sboettcher/lasertag/CADDesign/FinalDesigns/Handel/Griff_Akkuhalter.SLDPRT

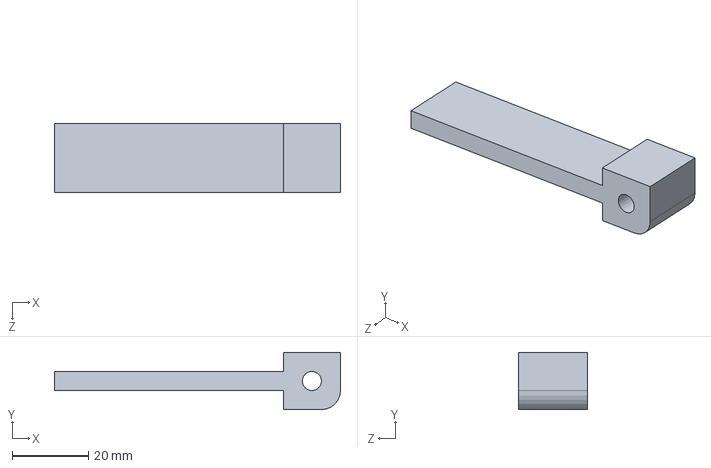
[picture p15: CAD file, 2015-03-04]
CADDesign/FinalDesigns/Handel/Griff_Akkuhalter.SLDPRT
75.0 x 15.0 x 18.0 mm
