sboettcher/lasertag/CADDesign/FinalDesigns/Other/Rohr.SLDPRT

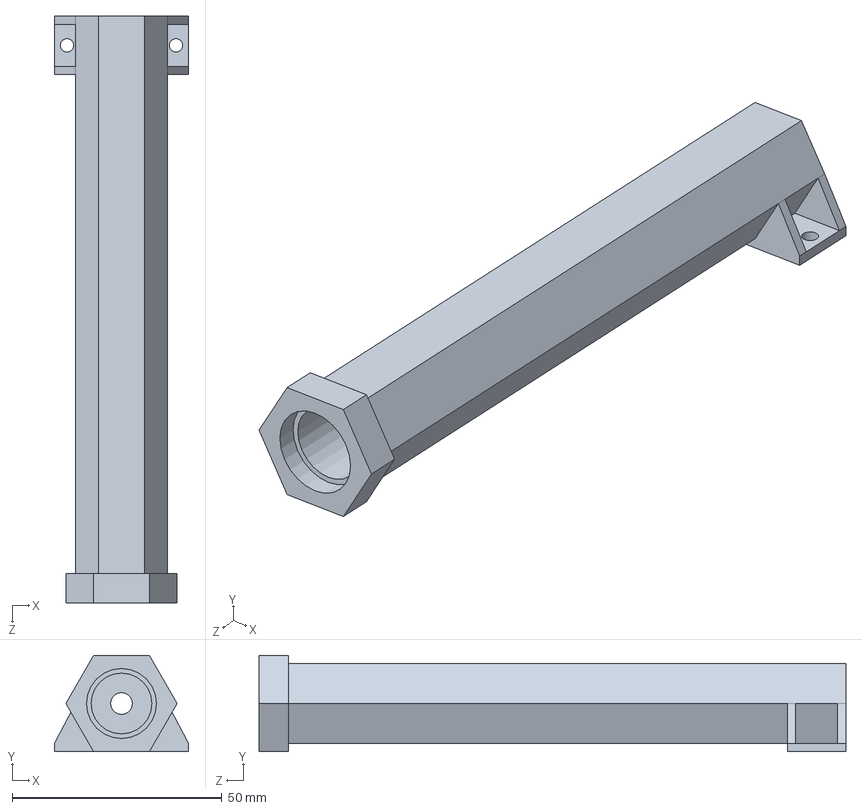
[picture p16: CAD file, 2015-03-04]
CADDesign/FinalDesigns/Other/Rohr.SLDPRT
32.0 x 23.0 x 140.0 mm
