sboettcher/lasertag/CADDesign/FinalDesigns/RFIDReader/Deckel.SLDPRT

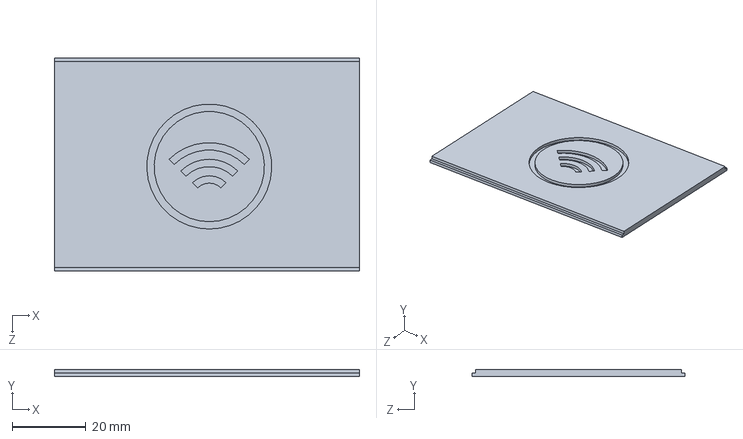
[picture p17: CAD file, 2015-03-04]
CADDesign/FinalDesigns/RFIDReader/Deckel.SLDPRT
83.0 x 2.00 x 58.0 mm
