sboettcher/lasertag/CADDesign/FinalDesigns/VestMaster/Gehaeuse.SLDPRT

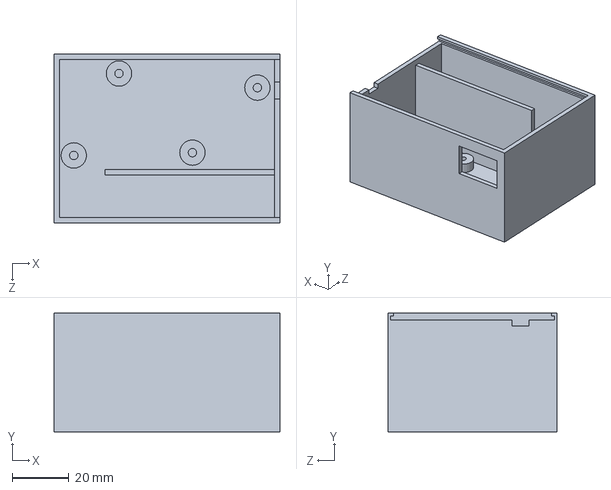
[picture p18: CAD file, 2015-03-04]
CADDesign/FinalDesigns/VestMaster/Gehaeuse.SLDPRT
80.0 x 42.0 x 60.0 mm
