sboettcher/lasertag/CADDesign/FinalDesigns/Components/Bluetooth_Tagger.SLDPRT

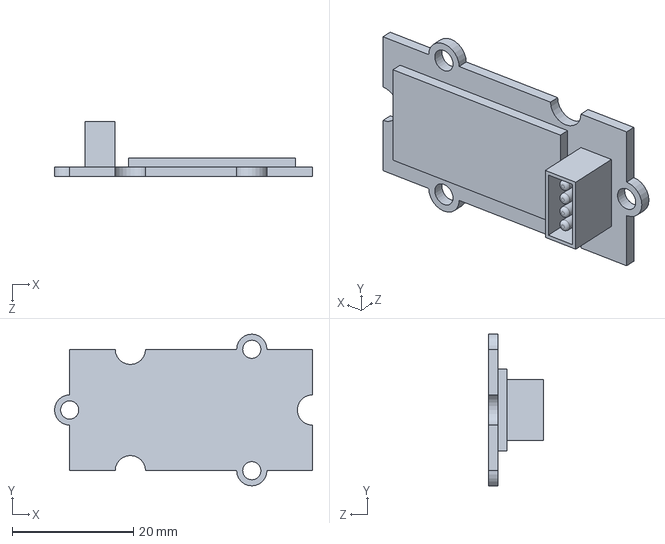
[picture p19: CAD file, 2015-03-04]
CADDesign/FinalDesigns/Components/Bluetooth_Tagger.SLDPRT
42.5 x 25.0 x 9.00 mm
