sboettcher/lasertag/CADDesign/FinalDesigns/Corpus/IRReceiver_Abdeckung.SLDPRT

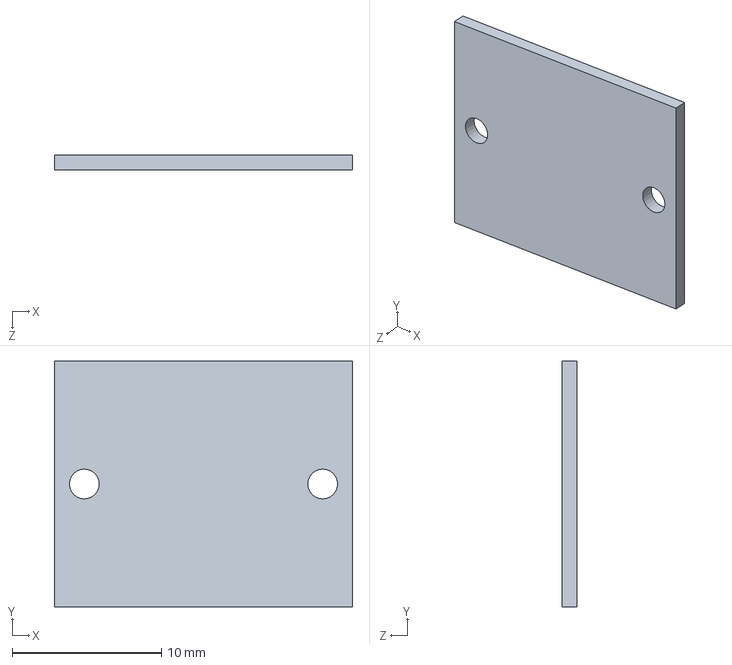
[picture p20: CAD file, 2015-03-04]
CADDesign/FinalDesigns/Corpus/IRReceiver_Abdeckung.SLDPRT
20.0 x 16.5 x 1.00 mm
