sboettcher/lasertag/CADDesign/FinalDesigns/DisplayHolder/Display_Holder_without_Tripod.SLDPRT

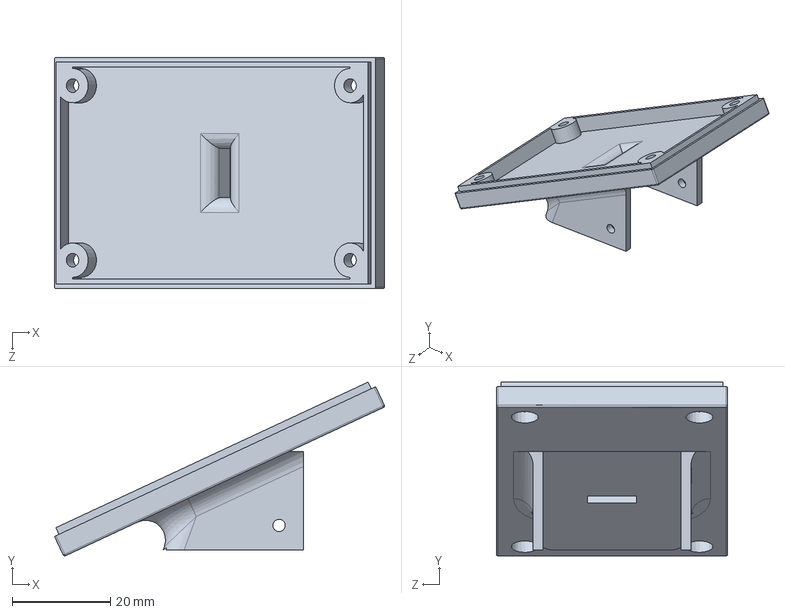
[picture p21: CAD file, 2015-03-04]
CADDesign/FinalDesigns/DisplayHolder/Display_Holder_without_Tripod.SLDPRT
67.0 x 35.3 x 47.0 mm
