sboettcher/lasertag/CADDesign/FinalDesigns/Handel/Griff_R_new.SLDPRT

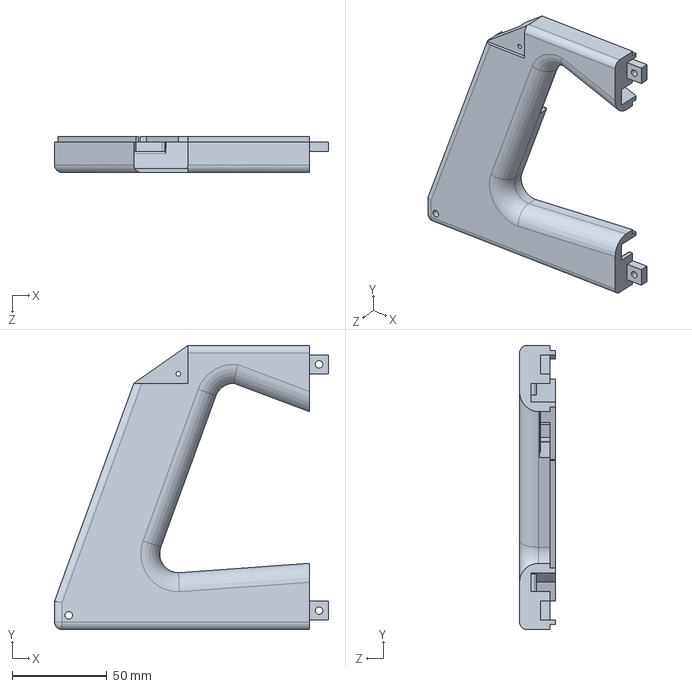
[picture p22: CAD file, 2015-03-04]
CADDesign/FinalDesigns/Handel/Griff_R_new.SLDPRT
144.6 x 150.0 x 19.0 mm
