sboettcher/lasertag/CADDesign/FinalDesigns/Other/Button.SLDPRT

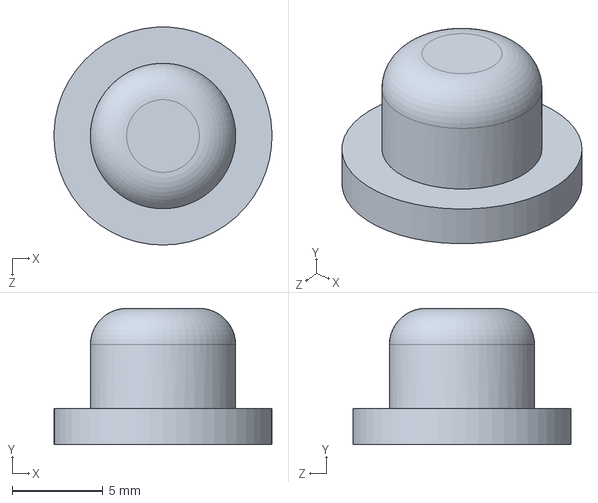
[picture p23: CAD file, 2015-03-04]
CADDesign/FinalDesigns/Other/Button.SLDPRT
12.0 x 7.50 x 12.0 mm
