sboettcher/lasertag/CADDesign/FinalDesigns/RailMount/RailMountKabel.SLDPRT

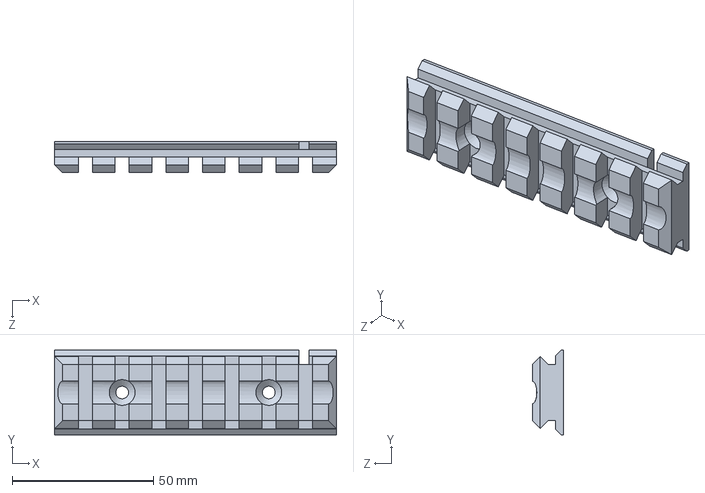
[picture p24: CAD file, 2015-03-04]
CADDesign/FinalDesigns/RailMount/RailMountKabel.SLDPRT
100.0 x 30.0 x 11.2 mm
