sboettcher/lasertag/CADDesign/FinalDesigns/VestMaster/Deckel.SLDPRT

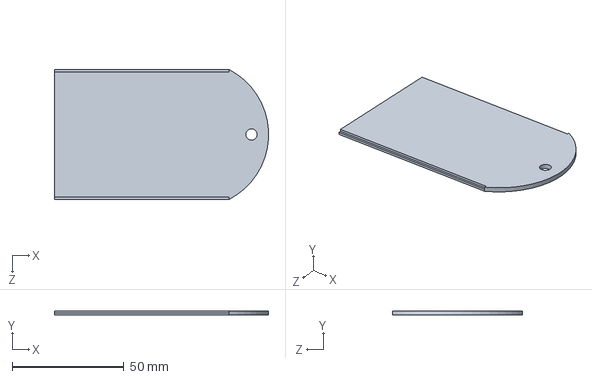
[picture p25: CAD file, 2015-03-04]
CADDesign/FinalDesigns/VestMaster/Deckel.SLDPRT
95.6 x 2.00 x 58.0 mm
