sboettcher/lasertag/CADDesign/FinalDesigns/Components/Display.SLDPRT

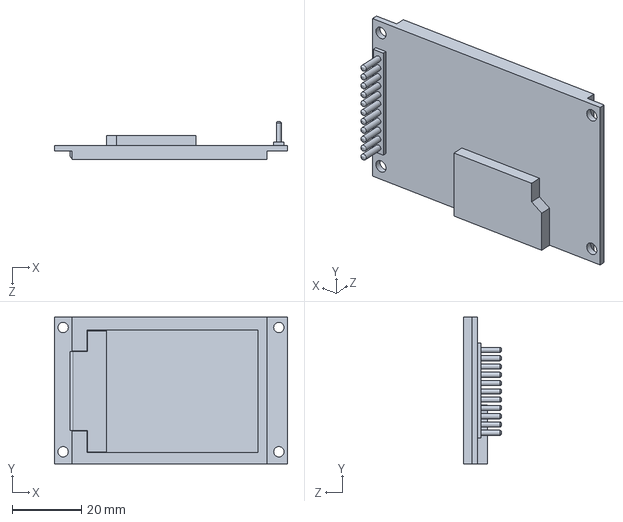
[picture p26: CAD file, 2015-03-04]
CADDesign/FinalDesigns/Components/Display.SLDPRT
67.5 x 42.5 x 11.0 mm
