sboettcher/lasertag/CADDesign/FinalDesigns/DisplayHolder/Display_Tripod.SLDPRT

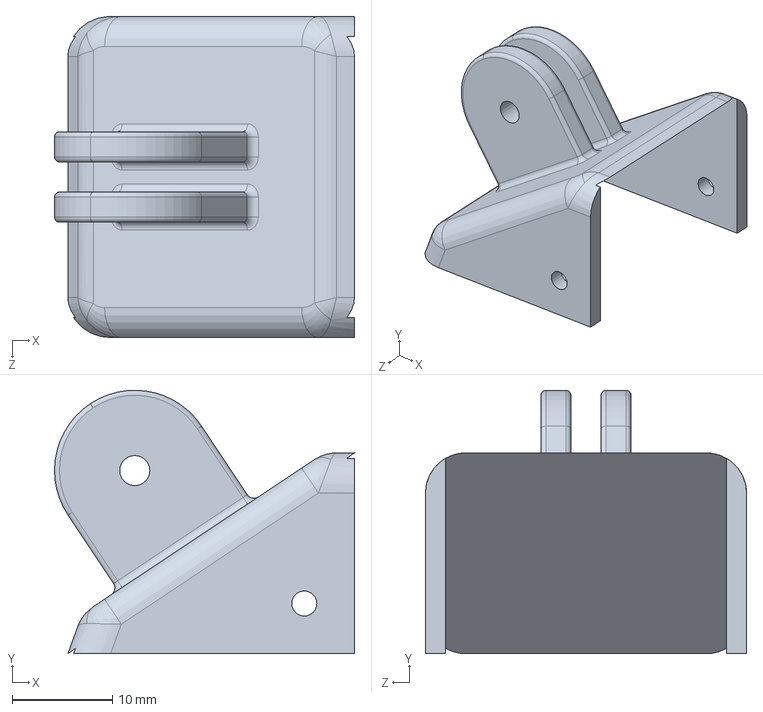
[picture p27: CAD file, 2015-03-04]
CADDesign/FinalDesigns/DisplayHolder/Display_Tripod.SLDPRT
29.9 x 26.2 x 32.0 mm
