sboettcher/lasertag/CADDesign/FinalDesigns/RailMount/RedDot-Sight2_Bottom.SLDPRT

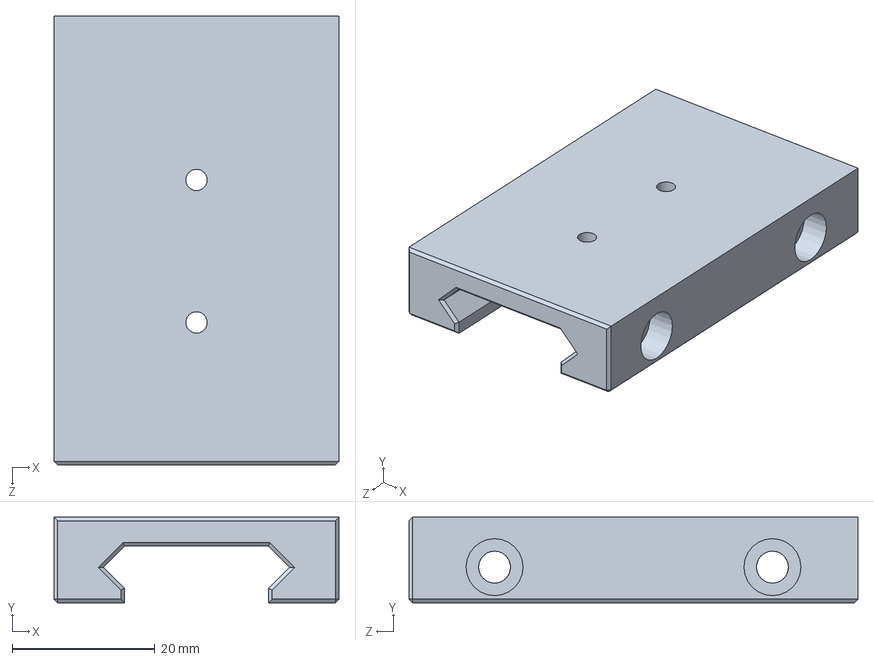
[picture p28: CAD file, 2015-03-04]
CADDesign/FinalDesigns/RailMount/RedDot-Sight2_Bottom.SLDPRT
40.0 x 12.0 x 63.0 mm
