sboettcher/lasertag/CADDesign/FinalDesigns/VestMaster/westMasterLid.SLDPRT

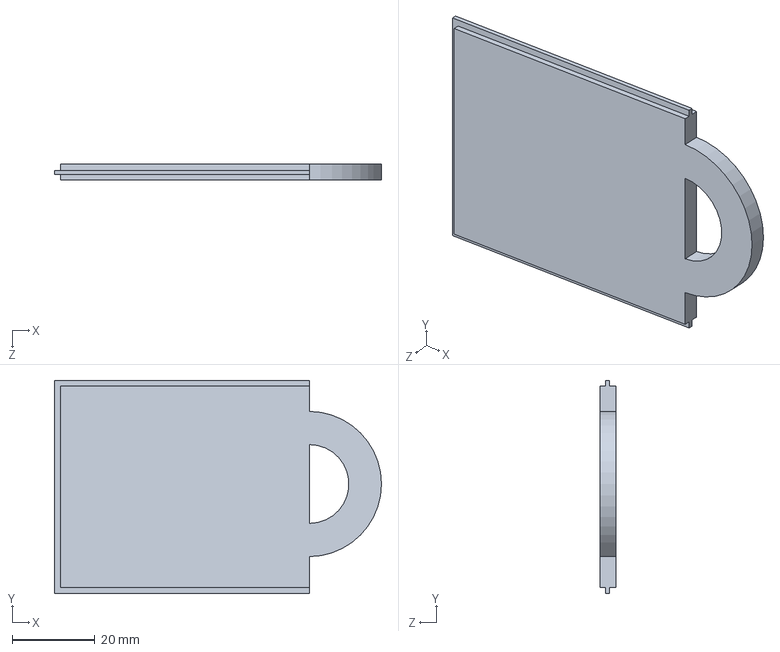
[picture p29: CAD file, 2015-03-04]
CADDesign/FinalDesigns/VestMaster/westMasterLid.SLDPRT
78.8 x 51.5 x 3.80 mm
