sboettcher/lasertag/CADDesign/FinalDesigns/RailMount/RedDot-Sight2_Top.SLDPRT

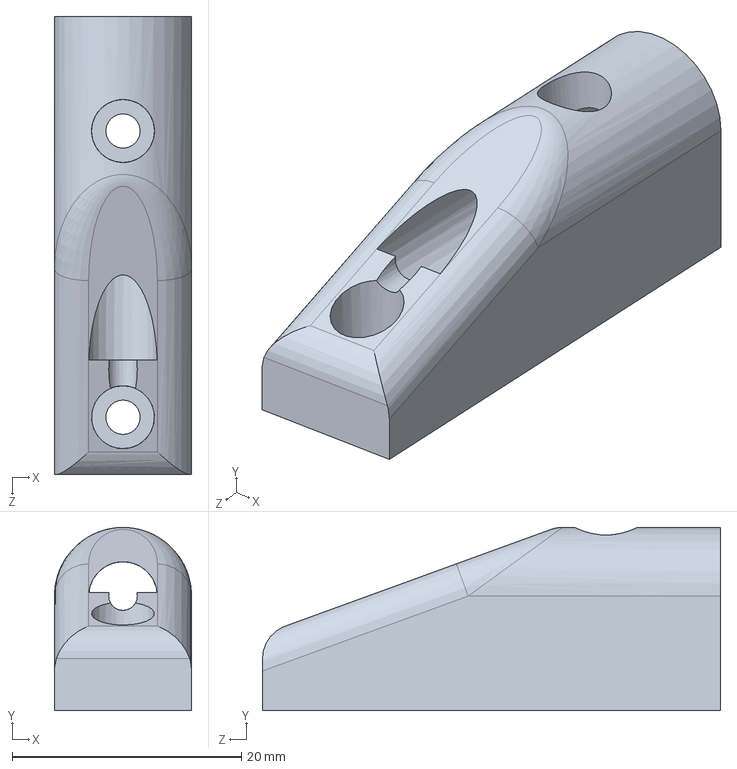
[picture p30: CAD file, 2015-03-04]
CADDesign/FinalDesigns/RailMount/RedDot-Sight2_Top.SLDPRT
12.0 x 16.0 x 40.0 mm
