sboettcher/lasertag/edison/src/lasertag.cpp

// Copyright 2015 Sebastian Boettcher

#include "./lasertag.h"

//________________________________________________________________________________
lasertag::lasertag()
  : m_dsp(NULL), m_i2c(NULL), m_gpio(NULL), m_bluetooth(NULL), m_client(NULL),
  m_i2c_bus(6), m_dsp_init(false), m_i2c_init(false),
  m_gpio_init(false), m_bt_init(false), m_tcp_init(false),
  m_bt_slave(""), m_active(false)
{
  m_hit_pos[0] = "Front";
  m_hit_pos[1] = "Back";
  m_hit_pos[2] = "Left";
  m_hit_pos[3] = "Right";
  m_hit_pos[100] = "Tagger";

  m_reset_time = 5;
}

//________________________________________________________________________________
lasertag::~lasertag() {
  delete m_i2c;
  delete m_gpio;
}



/*
 * I2C stuff
 */
 
//________________________________________________________________________________
void lasertag::i2c_init(int bus) {
  printf("[LASERTAG] init I2C on bus %d... ", m_i2c_bus);
  fflush(stdout);

  // make sure i2c bus number is 1 or 6
  if (bus != 1 && bus != 6) {
    printf("\n[LASERTAG] Wrong i2c bus number!. Using bus 6.\n");
  } else {
    m_i2c_bus = bus;
  }
  m_i2c = new mraa::I2c(m_i2c_bus);

  m_i2c_init = true;

  printf("Done.\n");
  fflush(stdout);

  i2c_write_int(I2C_BOOT, I2C_SEND_MSP);
}

//________________________________________________________________________________
uint8_t lasertag::i2c_read_int(uint8_t a) {
  if (!m_i2c_init)
    return 0;

  m_i2c->address(a);
  // read one integer from i2c bus and return it
  uint8_t rx_tx_buf[1];
  if (m_i2c->read(rx_tx_buf, 1) != 1) {
    printf("[LASERTAG] i2c read error!\n");
    fflush(stdout);
  }
  return rx_tx_buf[0];
  //return m_i2c->readByte();
}
//________________________________________________________________________________
void lasertag::i2c_write_int(uint8_t i, uint8_t a, bool start) {
  if (!m_i2c_init)
    return;

  m_i2c->address(a);
  if (start) {
    while(m_i2c->writeByte(I2C_START_BYTE) != MRAA_SUCCESS);
    usleep(100000);  // TODO: test if really necessary
  }
  while(m_i2c->writeByte(i) != MRAA_SUCCESS);
  usleep(100000);  // TODO: test if really necessary
  return;
}



/*
 * Display stuff
 */
 
//________________________________________________________________________________
void lasertag::dsp_init() {
  // constructor, init display, set rotation
  printf("[LASERTAG] init ILI9225... ");
  fflush(stdout);
  m_dsp = new TFT_22_ILI9225(TFT_CS_PIN, TFT_RST_PIN, TFT_RS_PIN);
  m_dsp->begin();
  m_dsp->setOrientation(0);
  printf("Done.\n");
  fflush(stdout);

  m_dsp_init = true;

  // draw the initial setup, fill status bars
  printf("[LASERTAG] draw init screen... ");
  fflush(stdout);
  dsp_draw_init();
  draw_health(0, m_player.get_max_health());
  draw_ammo(0, m_player.get_max_ammo());
  printf("Done.\n");
  fflush(stdout);
}

//________________________________________________________________________________
void lasertag::dsp_draw_init() {
  m_dsp->setFont(Terminal12x16);  // larger font

  //int fontX = m_dsp->fontX();
  int fontY = m_dsp->fontY();
  int maxX = m_dsp->maxX();
  int maxY = m_dsp->maxY();

  int barH = 25;

  m_h_coord[0] = 10;
  m_h_coord[1] = 35 + 3 * fontY;
  m_h_coord[2] = maxX - 10;
  m_h_coord[3] = m_h_coord[1] + barH;
  m_a_coord[0] = 10;
  m_a_coord[1] = m_h_coord[3] + 15 + fontY;
  m_a_coord[2] = maxX - 10;
  m_a_coord[3] = m_a_coord[1] + barH;

  // draw top part with placeholders for player name and current score
  m_dsp->drawText(10, 10, "[Player]");
  //m_dsp->drawText(maxX - 10 - 7 * fontX, 15 + fontY, "[Score]");
  m_dsp->drawText(10, 15 + fontY, "[Score]");
  m_dsp->drawLine(10, 20 + 2 * fontY, maxX - 10, 20 + 2 * fontY, COLOR_WHITE);

  // draw status bars
  m_dsp->drawText(10, 30 + 2 * fontY, "HEALTH:");
  m_dsp->drawRectangle(m_h_coord[0]-1, m_h_coord[1]-1, m_h_coord[2]+1, m_h_coord[3]+1, COLOR_WHITE);
  m_dsp->drawText(10, m_h_coord[3] + 10, "AMMO:");
  m_dsp->drawRectangle(m_a_coord[0]-1, m_a_coord[1]-1, m_a_coord[2]+1, m_a_coord[3]+1, COLOR_WHITE);

  // draw text boxes for hit, tagged status
  m_dsp->setFont(Terminal6x8);
  fontY = m_dsp->fontY();

  m_t_coord[0] = 10;
  m_t_coord[1] = m_a_coord[3] + 11 + fontY;
  m_t_coord[2] = maxX - 10;
  m_t_coord[3] = maxY - 5;

  m_dsp->drawText(10, m_a_coord[3] + 10, "hit by");
  m_dsp->drawText(maxX/2, m_a_coord[3] + 10, "tagged");
  m_dsp->drawRectangle(m_t_coord[0], m_t_coord[1], m_t_coord[2], m_t_coord[3], COLOR_WHITE);
  m_dsp->drawLine(maxX/2, m_t_coord[1], maxX/2, m_t_coord[3], COLOR_WHITE);
}



/*
 * other initializations
 */
 
//________________________________________________________________________________
void lasertag::bt_init() {
  if (m_bt_slave == "")
    return;

  m_bluetooth = new edison_serial("/dev/ttyMFD1", B38400);  // UART1, bt module needs 38400 baud
  m_bluetooth->bt_master_init("EdisonBTMaster01", m_bt_slave);
  
  printf("\n");
  fflush(stdout);

  m_threads.push_back(std::thread(&lasertag::t_read_bt, this));

  m_bt_init = true;
}

//________________________________________________________________________________
void lasertag::tcp_init(std::string address) {
  m_client = new tcp_client;
  if (m_client->tcp_connect(address))
    m_tcp_init = true;
}

//________________________________________________________________________________
void lasertag::gpio_init(int pin) {
  m_gpio = new mraa::Gpio(pin);
  if (m_gpio == NULL) {
    printf("[LASERTAG] gpio init failed.\n");
    fflush(stdout);
    return;
  }

  mraa_result_t response;
  response = m_gpio->dir(mraa::DIR_IN);
  if (response != MRAA_SUCCESS) {
    mraa::printError(response);
    return;
  }

  m_gpio_init = true;
}



/*
 * Functions called as threads. These handle all the IO stuff etc.
 */

//________________________________________________________________________________
void lasertag::t_read_i2c() {
  uint8_t i2c_rec = 0;

  std::vector<std::future<void>> handles;  // collect all handles for async calls
  while (m_active) {
    if (!m_i2c_init)
      continue;

    // read from rec i2c
    i2c_rec = i2c_read_int(I2C_REC_MSP);
    // filter out idle, error bytes
    if (i2c_rec != 0 && i2c_rec != 255) {
      // asynchronously call hitreg function so i2c communication can continue during
      handles.push_back(std::async(std::launch::async, &lasertag::hit_register, this, i2c_rec, 100));
    }

    // read from send i2c
    i2c_rec = i2c_read_int(I2C_SEND_MSP);
    //if (i2c_rec != 0) {
    //  printf("recieved %d\n", i2c_rec);
    //  fflush(stdout);
    //}
    if (i2c_rec == I2C_TRIGGER) {
      if (m_player.get_ammo() > 0) {
        // decrement ammo on trigger activation
        int old = m_player.fired();
        // asynchronously draw on display so tcp communication can continue
        handles.push_back(std::async(std::launch::async, &lasertag::draw_ammo, this, old, m_player.get_ammo()));
        // write current ammo to server
        std::stringstream ss;
        ss << "<as:" << m_player.get_ammo() << ">\n";
        if (m_tcp_init && m_client->connected())
          m_client->tcp_send(ss.str());
        if (m_player.get_ammo() == 0) {
          i2c_write_int(I2C_NO_AMMO, I2C_SEND_MSP);
          handles.push_back(std::async(std::launch::async, &lasertag::reset_ammo, this));
        }
      }
    }
    usleep(1000);
  }
  for (auto& h : handles) h.get();  // make sure all async calls return
}

//________________________________________________________________________________
void lasertag::t_read_bt() {
  int bt_rec = 0;
  int code = 0;
  int pos = 0;

  uint8_t idx = 0;

  std::vector<std::future<void>> handles;  // collect all handles for async calls
  while (m_active) {
    if (!m_bt_init || !m_bluetooth->bt_connected())
      continue;
    while (m_bluetooth->available(0,1000)) {
      // read byte from bluetooth serial
      bt_rec = (uint8_t)m_bluetooth->serial_read();
      if (bt_rec == SERIAL_START_BYTE) {  // indicates new hit, read next 2 bytes for code and position
        idx = 1;
      } else if (idx == 1) {
        code = bt_rec;
        idx = 2;
      } else if (idx == 2) {
        pos = bt_rec;
        idx = 0;
        // asynchronously call hitreg function so bt communication can continue during
        handles.push_back(std::async(std::launch::async, &lasertag::hit_register, this, code, pos));
      }
      bt_rec = 0;
    }
  }
  for (auto& h : handles) h.get();  // make sure all async calls return
}

//________________________________________________________________________________
void lasertag::t_read_tcp() {
  while (m_active) {
    if (!m_tcp_init || !m_client->connected())
      continue;
    if (m_client->tcp_available(0, 1000) > 0) {
      // read string from tcp, doesn't return terminating characters
      std::string tcp_rec = m_client->tcp_read_string("\n");
      parse_cmd(tcp_rec);
    }
  }
}

//________________________________________________________________________________
void lasertag::t_read_gpio() {
  std::vector<std::future<void>> handles;  // collect all handles for async calls
  while (m_active) {
    if (m_gpio_init && m_gpio->read() == 0) {
      if (m_player.get_ammo() > 0) {
        // decrement ammo on trigger activation
        int old = m_player.fired();
        // asynchronously draw on display so tcp communication can continue
        handles.push_back(std::async(std::launch::async, &lasertag::draw_ammo, this, old, m_player.get_ammo()));
      }
      usleep(100000);  // wait some time so tagger can't trigger continuously
    }
  }
  for (auto& h : handles) h.get();  // make sure all async calls return
}



/*
 * Threading management
 */
 
//________________________________________________________________________________
void lasertag::spawn_threads() {
  printf("[LASERTAG] Spawning threads.\n");
  fflush(stdout);
  m_active = true;
  m_threads.push_back(std::thread(&lasertag::t_read_i2c, this));
  //m_threads.push_back(std::thread(&lasertag::t_read_bt, this));  // only spawn if vest used
  m_threads.push_back(std::thread(&lasertag::t_read_tcp, this));
  //m_threads.push_back(std::thread(&lasertag::t_read_gpio, this));  // now handled by msp sending 's' via i2c
  printf("[LASERTAG] Done.\n");
  fflush(stdout);
}

//________________________________________________________________________________
void lasertag::join_threads() {
  printf("[LASERTAG] Joining threads.\n");
  fflush(stdout);
  m_active = false;
  for (auto& th : m_threads) th.join();
  m_threads.clear();
  printf("[LASERTAG] Done.\n");
  fflush(stdout);
}



/*
 * Gameplay functions
 */

//________________________________________________________________________________
void lasertag::hit_register(int code, int pos) {
  if (m_player.get_health() == 0)
    return;

  if (code == m_player.get_ID())
    return;

  // make sure there is only one execution of the function at a time
  std::lock_guard<std::recursive_mutex> hitreg_lock(m_mtx_hitreg);
  printf("[LASERTAG] Hit by %i at %i\n", code, pos);
  fflush(stdout);
  
  // send the player code to the server to recieve player name
  std::stringstream ss;
  ss << "<hi:" << code << ":" << pos << ">\n";
  if (m_tcp_init && m_client->connected())
    m_client->tcp_send(ss.str());

  // decrement health by one
  if (m_player.get_health() > 0) {
    int old = m_player.hit();
    draw_health(old, m_player.get_health());
  }

  // write hit position to display
  clear_hit_pos();
  std::stringstream text;
  //text << code << " -> " << pos;
  if (m_hit_pos.count(pos) == 0) {
    text << "N/A";
  } else {
    text << m_hit_pos[pos];
  }
  dsp_write(m_t_coord[0] + 5, m_t_coord[1] + 5, text.str());

  if (m_player.get_health() == 0) {
    i2c_write_int(I2C_NO_HEALTH, I2C_SEND_MSP);
    reset_health();
  }
}

//________________________________________________________________________________
void lasertag::parse_cmd(std::string cmd) {
  std::vector<std::future<void>> handles;  // collect all handles for async calls

  printf("%s\n", cmd.c_str());
  fflush(stdout);

  if (cmd.find("<") == std::string::npos || cmd.find(">") == std::string::npos)
    return;

  // command structure: <key:data>
  // get the command key
  std::string key = cmd.substr(cmd.find("<") + 1, cmd.find(":") - 1);

  // filter leading exclamation point from key that the server might send
  if (key.find("!") != std::string::npos)
    key = key.substr(key.find("!"), 1);

  if (key == "")
    return;

  // get the command data
  std::string data = cmd.substr(cmd.find(":") + 1, cmd.find(">") - 1 - cmd.find(":"));
  if (data == "")
    return;

  if (key == "ci") {  // <ci:has_vest:id>
    m_player.set_vest(std::stoi(data.substr(0, 1)));
    m_player.set_ID(std::stoi(data.substr(2)));
    std::stringstream ss;
    ss << "vest" << std::to_string(m_player.get_ID());
    m_bt_slave = ss.str();
    if (m_player.get_vest()) {
      bt_init();
      usleep(2000000);  // 2 sec wait for safety, might not be needed
      set_team_color(m_player.get_color());
    }
    // transmit ID to msp
    if (m_i2c_init) {
      i2c_write_int(I2C_PLAYER_CODE, I2C_SEND_MSP);
      i2c_write_int(m_player.get_ID(), I2C_SEND_MSP, false);
      //i2c_write_int(0xFF, I2C_REC_MSP, false);
      //i2c_write_int(0x00, I2C_REC_MSP, false);
      //i2c_write_int(m_player.get_ID(), I2C_REC_MSP, false);
      //i2c_write_int(0xFE, I2C_REC_MSP, false);
    }
  } else if (key == "np") {  // <np:playername>
    m_player.set_name(data);
    write_name();
  } else if (key == "in") {
    write_info(data, 2);
    write_name();
  } else if (key == "ts") {  // <ts:teamcolor>
    if (data == "red") {
      m_player.set_color(COLOR_RED);
    } else if (data == "green") {
      m_player.set_color(COLOR_GREEN);
    } else if (data == "blue") {
      m_player.set_color(COLOR_BLUE);
    } else if (data == "none") {
      m_player.set_color(COLOR_WHITE);
    }
    set_team_color(m_player.get_color());
    write_name();
  } else if (key == "hs") {  // <hs:health>
    int old = m_player.set_health(std::stoi(data));
    draw_health(old, m_player.get_health());
  } else if (key == "ps") {  // <ps:score>
    m_player.set_score(std::stoi(data));
    write_score();
  } else if (key == "as") {  // <as:ammo>
    int old = m_player.set_ammo(std::stoi(data));
    draw_ammo(old, m_player.get_ammo());
  } else if (key == "ap") {  // <ap:ammo_per>
    m_player.set_ammo_per(std::stoi(data));
  } else if (key == "hd") {  // <hd:health_decrease>
    m_player.set_health_per(std::stoi(data));
  } else if (key == "hi") {  // <hi:tagged:pos>
    std::string name = data.substr(0, data.find(":"));
    std::string pos = data.substr(data.find(":") + 1);
    printf("[LASERTAG] Tagged player %s at %s\n", name.c_str(), pos.c_str());
    fflush(stdout);
    clear_tagged_pos();
    clear_tagged_name();
    // asynchronously draw on display so tcp communication can continue
    // TODO: check for string length, should fit in box
    handles.push_back(std::async(std::launch::async, &lasertag::dsp_write, this, m_dsp->maxX()/2 + 5, m_t_coord[1] + 5, pos, Terminal6x8, COLOR_WHITE));
    handles.push_back(std::async(std::launch::async, &lasertag::dsp_write, this, m_dsp->maxX()/2 + 5, m_t_coord[1] + 15, name, Terminal11x16, COLOR_WHITE));
  } else if (key == "hp") {  // <hp:hit_by>
    printf("[LASERTAG] Hit by %s \n", data.c_str());
    fflush(stdout);
    clear_hit_name();
    // asynchronously draw on display so tcp communication can continue
    // TODO: check for string length, should fit in box
    handles.push_back(std::async(std::launch::async, &lasertag::dsp_write, this, m_t_coord[0] + 5, m_t_coord[1] + 15, data, Terminal11x16, COLOR_WHITE));
  } else if (key == "hv") {  // <hv:tagged_name>
    printf("[LASERTAG] Tagged player %sn", data.c_str());
    fflush(stdout);
    clear_tagged_name();
    // asynchronously draw on display so tcp communication can continue
    // TODO: check for string length, should fit in box
    handles.push_back(std::async(std::launch::async, &lasertag::dsp_write, this, m_dsp->maxX()/2 + 5, m_t_coord[1] + 15, data, Terminal11x16, COLOR_WHITE));
  } else if (key == "at") {  // <at:tagger_active>
    if (data == "0") {
      i2c_write_int(I2C_DEACTIVATE, I2C_SEND_MSP);
    } else if (data == "1") {
      i2c_write_int(I2C_ACTIVATE, I2C_SEND_MSP);
    }
  } else {
    printf("[LASERTAG] server command not recognized: %s\n", cmd.c_str());
    fflush(stdout);
  }

  // this doesn't make sense here since parse_cmd should return as quickly as possible (don't block caller),
  // so we can't wait for the longer display draw functions to return.
  // Can we still somehow make sure all async called functions return?
  //for (auto& h : handles) h.get();  // make sure all async calls return
}


//________________________________________________________________________________
void lasertag::set_team_color(uint16_t color) {
  if (m_bt_init) {
    m_bluetooth->serial_write(SERIAL_START_BYTE);
    switch (color) {
      case COLOR_RED: m_bluetooth->serial_write(1); break;
      case COLOR_GREEN: m_bluetooth->serial_write(2); break;
      case COLOR_BLUE: m_bluetooth->serial_write(4); break;
      case COLOR_WHITE: m_bluetooth->serial_write(7); break;
    }
  }
  if (m_i2c_init) {
    i2c_write_int(I2C_TEAM_COLOR, I2C_SEND_MSP);
    // send RGB values
    switch (color) {
      case COLOR_RED: i2c_write_int(I2C_COLOR_BRIGHT, I2C_SEND_MSP, false);
                      i2c_write_int(0, I2C_SEND_MSP, false);
                      i2c_write_int(0, I2C_SEND_MSP, false);
                      break;
      case COLOR_GREEN: i2c_write_int(0, I2C_SEND_MSP, false);
                        i2c_write_int(I2C_COLOR_BRIGHT, I2C_SEND_MSP, false);
                        i2c_write_int(0, I2C_SEND_MSP, false);
                        break;
      case COLOR_BLUE: i2c_write_int(0, I2C_SEND_MSP, false);
                       i2c_write_int(0, I2C_SEND_MSP, false);
                       i2c_write_int(I2C_COLOR_BRIGHT, I2C_SEND_MSP, false);
                       break;
      case COLOR_WHITE: i2c_write_int(I2C_COLOR_BRIGHT, I2C_SEND_MSP, false);
                        i2c_write_int(I2C_COLOR_BRIGHT, I2C_SEND_MSP, false);
                        i2c_write_int(I2C_COLOR_BRIGHT, I2C_SEND_MSP, false);
                        break;
    }
  }
}


//________________________________________________________________________________
void lasertag::reset_health() {
  printf("[LASERTAG] resetting health... ");
  fflush(stdout);
  usleep(m_reset_time * 1000000);
  // make sure send msp actually gets the command (send 3x, kind of a hack...)
  if (m_i2c_init) {
    i2c_write_int(I2C_FULL_HEALTH, I2C_SEND_MSP);
    i2c_write_int(I2C_FULL_HEALTH, I2C_SEND_MSP);
    i2c_write_int(I2C_FULL_HEALTH, I2C_SEND_MSP);
  }
  draw_health(m_player.refill_health(-1), m_player.get_max_health());
  // write current health to server
  std::stringstream ss;
  ss << "<hs:" << m_player.get_health() << ">\n";
  if (m_tcp_init && m_client->connected())
    m_client->tcp_send(ss.str());
  printf("Done.\n");
  fflush(stdout);
}
//________________________________________________________________________________
void lasertag::reset_ammo() {
  printf("[LASERTAG] resetting ammo... ");
  fflush(stdout);
  usleep(m_reset_time * 1000000);
  // make sure send msp actually gets the command (send 3x, kind of a hack...)
  if (m_i2c_init) {
    i2c_write_int(I2C_FULL_AMMO, I2C_SEND_MSP);
    i2c_write_int(I2C_FULL_AMMO, I2C_SEND_MSP);
    i2c_write_int(I2C_FULL_AMMO, I2C_SEND_MSP);
  }
  draw_ammo(m_player.reload(-1), m_player.get_max_ammo());
  // write current ammo to server
  std::stringstream ss;
  ss << "<as:" << m_player.get_ammo() << ">\n";
  if (m_tcp_init && m_client->connected())
    m_client->tcp_send(ss.str());
  printf("Done.\n");
  fflush(stdout);
}




/*
 * Display control functions
 * All functions must make sure only one draws to the display at a time.
 */
 
//________________________________________________________________________________
void lasertag::clear_hit_pos() {
  if (!m_dsp_init)
    return;
  std::lock_guard<std::recursive_mutex> dsp_lock(m_mtx_dsp);
  m_dsp->fillRectangle(m_t_coord[0]+5, m_t_coord[1]+5, m_dsp->maxX()/2-1, m_t_coord[1]+5+8, COLOR_BLACK);
}
//________________________________________________________________________________
void lasertag::clear_hit_name() {
  if (!m_dsp_init)
    return;
  std::lock_guard<std::recursive_mutex> dsp_lock(m_mtx_dsp);
  m_dsp->fillRectangle(m_t_coord[0]+5, m_t_coord[1]+15, m_dsp->maxX()/2-1, m_t_coord[1]+15+16, COLOR_BLACK);
}

//________________________________________________________________________________
void lasertag::clear_tagged_pos() {
  if (!m_dsp_init)
    return;
  std::lock_guard<std::recursive_mutex> dsp_lock(m_mtx_dsp);
  m_dsp->fillRectangle(m_dsp->maxX()/2+5, m_t_coord[1]+5, m_t_coord[2]-1, m_t_coord[1]+5+8, COLOR_BLACK);
}
//________________________________________________________________________________
void lasertag::clear_tagged_name() {
  if (!m_dsp_init)
    return;
  std::lock_guard<std::recursive_mutex> dsp_lock(m_mtx_dsp);
  m_dsp->fillRectangle(m_dsp->maxX()/2+5, m_t_coord[1]+15, m_t_coord[2]-1, m_t_coord[1]+15+16, COLOR_BLACK);
}


//________________________________________________________________________________
void lasertag::dsp_write(int x, int y, std::string text, uint8_t* font, uint16_t color) {
  if (!m_dsp_init)
    return;
  std::lock_guard<std::recursive_mutex> dsp_lock(m_mtx_dsp);

  // reset font to the previous one after draw
  uint8_t tmp = m_dsp->setFont(font);
  m_dsp->drawText(x, y, text, color);
  m_dsp->setFont(&tmp);
}

//________________________________________________________________________________
void lasertag::draw_health(int old_h, int new_h) {
  std::lock_guard<std::recursive_mutex> dsp_lock(m_mtx_dsp);

  // calculate the correct horizontal coordinates for the rectangle start and end point
  float perc_old = old_h * (1.0 / m_player.get_max_health());
  float perc_new = new_h * (1.0 / m_player.get_max_health());
  int h_old = ((m_h_coord[2] - m_h_coord[0]) * perc_old) + m_h_coord[0];
  int h_new = ((m_h_coord[2] - m_h_coord[0]) * perc_new) + m_h_coord[0];

  uint8_t led = 7 * perc_new;
  if (led < 1)
    led = 1;
  i2c_write_int(48 + led, I2C_SEND_MSP);

  if (!m_dsp_init)
    return;

  // black if decrement, color if increment
  if (h_old > h_new) {
    m_dsp->fillRectangle(h_new, m_h_coord[1], h_old, m_h_coord[3], COLOR_BLACK);
  } else if (h_old < h_new) {
    m_dsp->fillRectangle(h_old, m_h_coord[1], h_new, m_h_coord[3], COLOR_RED);
  }
}

//________________________________________________________________________________
void lasertag::draw_ammo(int old_a, int new_a) {
  if (!m_dsp_init)
    return;
  std::lock_guard<std::recursive_mutex> dsp_lock(m_mtx_dsp);

  // calculate the correct horizontal coordinates for the rectangle start and end point
  float perc_old = old_a * (1.0 / m_player.get_max_ammo());
  float perc_new = new_a * (1.0 / m_player.get_max_ammo());
  int a_old = ((m_a_coord[2] - m_a_coord[0]) * perc_old) + m_a_coord[0];
  int a_new = ((m_a_coord[2] - m_a_coord[0]) * perc_new) + m_a_coord[0];

  // black if decrement, color if increment
  if (a_old > a_new) {
    m_dsp->fillRectangle(a_new, m_a_coord[1], a_old, m_a_coord[3], COLOR_BLACK);
  } else if (a_old < a_new) {
    m_dsp->fillRectangle(a_old, m_a_coord[1], a_new, m_a_coord[3], COLOR_GREEN);
  }
}

//________________________________________________________________________________
void lasertag::write_name() {
  if (!m_dsp_init)
    return;
  std::lock_guard<std::recursive_mutex> dsp_lock(m_mtx_dsp);

  m_dsp->fillRectangle(10, 10, m_dsp->maxX()-10, 26, COLOR_BLACK);
  uint8_t tmp = m_dsp->setFont(Terminal12x16);
  m_dsp->drawText(10, 10, m_player.get_name(), m_player.get_color());
  m_dsp->setFont(&tmp);
}

//________________________________________________________________________________
void lasertag::write_score() {
  if (!m_dsp_init)
    return;
  std::lock_guard<std::recursive_mutex> dsp_lock(m_mtx_dsp);

  m_dsp->fillRectangle(10, 31, m_dsp->maxX()-10, 47, COLOR_BLACK);
  uint8_t tmp = m_dsp->setFont(Terminal12x16);
  m_dsp->drawText(10, 31, std::to_string(m_player.get_score()), COLOR_WHITE);
  m_dsp->setFont(&tmp);
}

//________________________________________________________________________________
void lasertag::write_info(std::string info, int sec) {
  if (!m_dsp_init)
    return;
  std::lock_guard<std::recursive_mutex> dsp_lock(m_mtx_dsp);

  m_dsp->fillRectangle(10, 10, m_dsp->maxX()-10, 26, COLOR_BLACK);
  uint8_t tmp = m_dsp->setFont(Terminal6x8);
  m_dsp->drawText(10, 10, info.substr(0, 26));
  if (info.size() > 26)
    m_dsp->drawText(10, 18, info.substr(26, 26));
  m_dsp->setFont(&tmp);

  usleep(sec * 1000000);
}
