sboettcher/lasertag/edison/include/lasertag.h

// Copyright 2015 Sebastian Boettcher

#include <stdio.h>
#include <stdlib.h>
#include <unistd.h>

#include <mraa.hpp>

#include <vector>
#include <map>
#include <string>
#include <sstream>
#include <iostream>
#include <thread>
#include <mutex>
#include <future>

#include "./TFT_22_ILI9225.h"
#include "./edison_serial.h"
#include "./tcp_client.h"
#include "./player.h"

#define I2C_BUS 6
#define TFT_CS_PIN 0
#define TFT_RST_PIN 32
#define TFT_RS_PIN 47

#define SERIAL_START_BYTE 0x7E
#define I2C_START_BYTE 0x7E

#define I2C_SEND_MSP 0x61
#define I2C_REC_MSP 0x68

#define I2C_BOOT 101  // 'e'
#define I2C_TRIGGER 115  // 's'
#define I2C_PLAYER_CODE 99  // 'c'
#define I2C_NO_HEALTH 100  // 'd'
#define I2C_NO_AMMO 97  // 'a'
#define I2C_FULL_HEALTH 104  // 'h'
#define I2C_FULL_AMMO 114  // 'r'
#define I2C_ACTIVATE 121  // 'y'
#define I2C_DEACTIVATE 120  // 'x'
#define I2C_TEAM_COLOR 116  // 't'

#define I2C_COLOR_BRIGHT 50

class lasertag {
  public:
    // constructor
    lasertag();
    // destructor
    ~lasertag();

    // initialize i2c on bus
    void i2c_init(int bus);
    // read uint8 from i2c address
    uint8_t i2c_read_int(uint8_t a);
    // write start byte and uint8_t to i2c address
    void i2c_write_int(uint8_t i, uint8_t a, bool start = true);

    // initializes some display stuff
    void dsp_init();
    void dsp_draw_init();
    // initialize bluetooth master
    void bt_init();
    // initialize tcp client server connection
    void tcp_init(std::string address);
    // initialize trigger gpio input
    void gpio_init(int pin);

    // threading
    void spawn_threads();
    void join_threads();

    // getter/setter functions
    mraa::I2c* i2c() {
      return m_i2c;
    }
    TFT_22_ILI9225* dsp() {
      return m_dsp;
    }
    edison_serial* bt() {
      return m_bluetooth;
    }
    tcp_client* tcp() {
      return m_client;
    }
    void set_bt_slave(std::string slave) {
      m_bt_slave = slave;
    }

  private:
    // register a hit, manage related stuff
    void hit_register(int code, int pos);

    // writes text to coordinates on display
    // if a font is given, the old one will be restored when the function returns
    void dsp_write(int x, int y, std::string text, uint8_t* font = Terminal6x8, uint16_t color = COLOR_WHITE);

    // draw the difference of the arguments given on the status bars
    void draw_health(int old_h, int new_h);
    void draw_ammo(int old_a, int new_a);

    // clear the corresponding text boxes on the display
    void clear_hit_pos();
    void clear_hit_name();
    void clear_tagged_pos();
    void clear_tagged_name();

    // read from i2c, threaded
    void t_read_i2c();
    // read from bluetooth, threaded
    void t_read_bt();
    // read from tcp server, threaded
    void t_read_tcp();
    // read from trigger gpio pin, threaded
    void t_read_gpio();

    // parse a command coming i.e. from the server and do the corresponding action
    void parse_cmd(std::string cmd);

    // transmits the team color to the vest via bt
    void set_team_color(uint16_t color);

    // write name and score to dsp
    void write_name();
    void write_score();
    // clear name, write info string instead, block number of seconds
    void write_info(std::string info, int sec);

    // reset health/ammo after certain amount of time
    void reset_health();
    void reset_ammo();

    
    //________________________________________________________________________________
    TFT_22_ILI9225* m_dsp;
    mraa::I2c* m_i2c;
    mraa::Gpio* m_gpio;
    edison_serial* m_bluetooth;
    tcp_client* m_client;

    int m_i2c_bus;

    bool m_dsp_init;
    bool m_i2c_init;
    bool m_gpio_init;
    bool m_bt_init;
    bool m_tcp_init;

    std::string m_bt_slave;

    std::vector<std::thread> m_threads;
    bool m_active;
    std::recursive_mutex m_mtx_hitreg;
    std::recursive_mutex m_mtx_dsp;

    uint16_t m_h_coord[4];
    uint16_t m_a_coord[4];
    uint16_t m_t_coord[4];

    Player m_player;
    int m_reset_time;

    std::map<uint8_t,std::string> m_hit_pos;
};
