sboettcher/lasertag/edison/include/player.h

#ifndef LASERTAG_PLAYER_H
#define LASERTAG_PLAYER_H

#include <string>

#define HIT_LOST_PERCENT 10
#define FULL_HEALTH 100
#define FULL_AMMO 50

#define MAX_NAME_LENGTH 10

class Player {
  public:
    // Constructor
    Player();
    
    // refill certain amount of ammo, return old value
    int reload(int amount);
    
    // refill certain amount of health, return old value
    int refill_health(int amount);
    
    // If Player got hit he will loose a defined amount of health
    // returns old value
    int hit();
    
    // If Player fires tagger he will loose 1 ammunition
    // returns old value
    int fired();

    // If Player tags someone increment score
    // returns old value
    int scored();

    
    // setter/getter
    int get_health() {return m_health;}
    int set_health(int health);
    int get_max_health() {return m_full_health;}
    int set_max_health(int health);
    int get_ammo() {return m_ammo;}
    int set_ammo(int ammo);
    int get_max_ammo() {return m_full_ammo;}
    int set_max_ammo(int ammo);

    void set_health_per(int health_per) {m_health_lost_per = health_per;}
    void set_ammo_per(int ammo_per) {m_ammo_lost_per = ammo_per;}
    
    void set_ID(int id) {m_id = (uint8_t) id;}
    uint8_t get_ID() {return m_id;}
    
    void set_name(std::string name) {m_name = name;}
    std::string get_name() {return m_name;}
    
    void set_color(uint16_t color) {m_color = color;}
    uint16_t get_color() {return m_color;}
    
    void set_score(int score) {m_score = score;}
    int get_score() {return m_score;}

    void set_vest(bool vest) {m_vest = vest;}
    int get_vest() {return m_vest;}
  
  private:
    // member vars
    uint8_t m_id;
    int m_score;
    int m_health;
    int m_full_health;
    int m_ammo;
    int m_full_ammo;
    uint16_t m_color;
    std::string m_name;
    bool m_vest;
    int m_health_lost_per;
    int m_ammo_lost_per;
    int m_score_per;
};

#endif
