sboettcher/lasertag/edison/include/edison_serial.h

// Copyright 2014 Sebastian Boettcher

#include <fcntl.h>
#include <errno.h>
#include <string.h>
#include <termios.h>
#include <time.h>
#include <stdio.h>
#include <stdlib.h>
#include <unistd.h>

#include <string>


class edison_serial {
  public:
    // constructor, takes the serial port (/dev/...) and baud rate (e.g. B9600)
    edison_serial(std::string port, speed_t baud);
    ~edison_serial();

    // send bt slave initiation
    void bt_slave_init(std::string name);
    // send bt master initiation and inquire for given slave
    void bt_master_init(std::string name, std::string slave);

    // wait for available data on port, false if timeout (sec) or error
    bool available(int sec, int usec = 0);
    // read one byte of data and return it
    char serial_read();
    // write the given string to port
    void serial_write(std::string s);

    // write the char to port
    void serial_write(char c);

    int get_serial_fd() {
      return m_fd;
    }

    bool bt_connected() {
      return m_bt_connected;
    }

  private:
    // open and configure given port
    bool open_port();
    void configure_port(speed_t baud);

    std::string m_port;
    int m_fd; // file description for serial port
    bool m_port_ready;
    bool m_bt_connected;
};
