sboettcher/lasertag/edison/bt_serial.h

// Copyright 2014 Sebastian Boettcher

#include <fcntl.h>
#include <errno.h>
#include <termios.h>
#include <time.h>
#include <stdio.h>
#include <stdlib.h>
#include <unistd.h>

#include <string>


class bt_serial {
  public:
    // constructor, takes the serial port (/dev/...)
    bt_serial(std::string port);
    ~bt_serial();

    void init();
    bool available(int timeout);
    char bt_read();
    void bt_write(std::string s);

    int get_serial_fd();

  private:
    bool open_port();
    void configure_port();

    std::string m_port;
    int m_fd; // file description for serial port
};
