sboettcher/lasertag/edison/src/groveOLEDtest.cpp

// Copyright 2014 Sebastian Boettcher

#include <signal.h>
#include <stdio.h>
#include <stdlib.h>
#include <unistd.h>
#include <syslog.h>

#include <mraa.hpp>
#include <ssd1327.h>

#include <iostream>
#include <string>

#define BUS_NUMBER 1

int running = 1;

void sig_handler(int signo) {
  if (signo == SIGINT) {
    printf("\nclosing nicely\n");
    running = 0;
  }
}

int main(int argc, char** argv) {
  // signal(SIGINT, sig_handler);

  printf("initialising on bus %d... ", BUS_NUMBER);
  fflush(stdout);
  upm::SSD1327* lcd = new upm::SSD1327(BUS_NUMBER);
  printf("done.\n");
  fflush(stdout);

  for (uint8_t i = 0; i < 12; ++i) {
    lcd->setCursor(i, 0);
    lcd->setGrayLevel(i);
    lcd->write("Hello World");
    printf("Hello World\n");
    fflush(stdout);
  }

  printf("closing... ");
  fflush(stdout);
  lcd->close();
  printf("done.\n");
  fflush(stdout);

  return 0;
}
